ErikOSorensen/inverse_riaa/design/iriaa.asc

C1: cap; 3n6
C2: cap; 1n
R1: res; {rin}
R2: res; 100k
R3: res; 883333
R4: res; 75k
R5: res; 560
R6: res; 41
V1: voltage; SINE(0 1 1k); AC 1
Named nets: 0, MM, MC, in
.ac dec 100 20 200000
.param rin 100
